flooddog/Flood-Dog-Github/Pressure Board Plate/Prerssure Mount.3mf

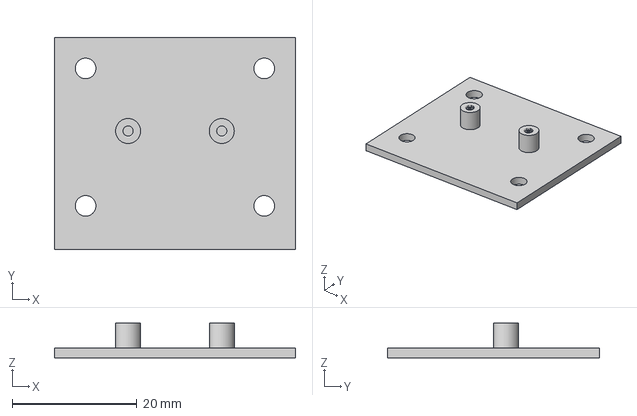
[picture p21: CAD file, 2021-11-01]
Pressure Board Plate/Prerssure Mount.3mf
38.6 x 34.0 x 5.57 mm
