flooddog/Flood-Dog-Github/Project Case_Flood Dog/Badge/Badge Template v57 v5.3mf

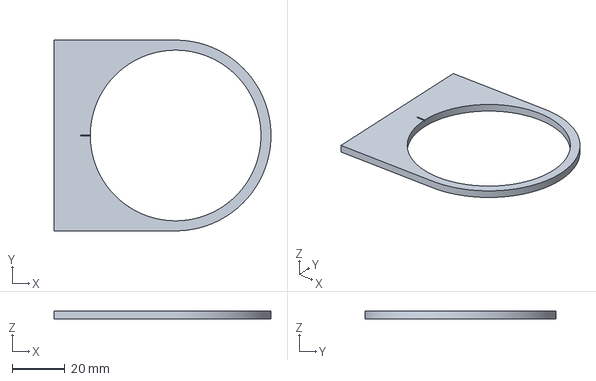
[picture p22: CAD file, 2021-12-22]
Project Case_Flood Dog/Badge/Badge Template v57 v5.3mf
81.9 x 72.0 x 3.00 mm
