flooddog/Flood-Dog-Github/Project Case_Flood Dog/Project Case_Flood Dog v53/Project Case_Flood Dog v53 v1_Left Cable Gland Cap.3mf

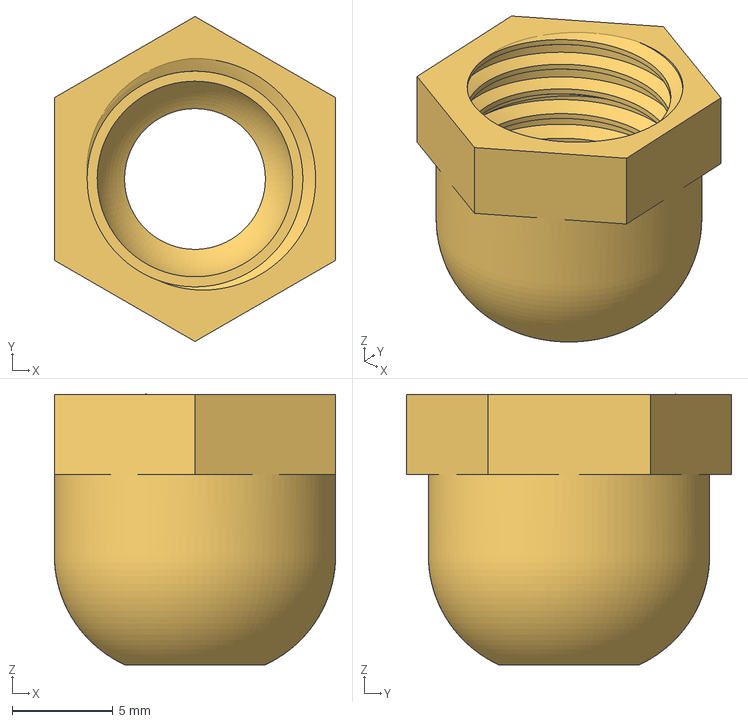
[picture p23: CAD file, 2021-11-01]
Project Case_Flood Dog/Project Case_Flood Dog v53/Project Case_Flood Dog v53 v1_Left Cable Gland Cap.3mf
14.0 x 16.2 x 13.5 mm
