flooddog/Flood-Dog-Github/Voltaics Solar Panel Frame/Voltaic Frame.3mf

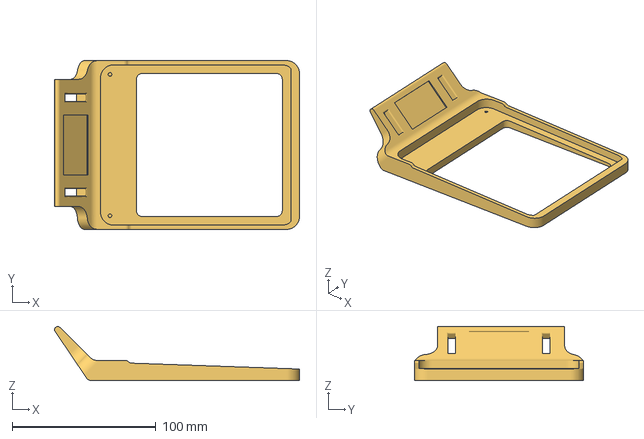
[picture p24: CAD file, 2021-11-01]
Voltaics Solar Panel Frame/Voltaic Frame.3mf
170.5 x 117.5 x 37.6 mm
