flooddog/Flood-Dog-Github/Capacitive Sensor Probe v2 v11/Component1_Cap Sensor v2 v11_Shell Top_FusionComponent.stl

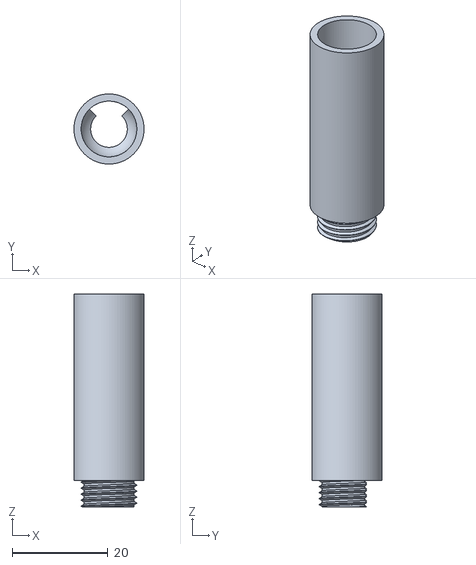
[picture p25: CAD file, 2021-06-04]
Capacitive Sensor Probe v2 v11/Component1_Cap Sensor v2 v11_Shell Top_FusionComponent.stl
14.6 x 14.6 x 44.5
