flooddog/Flood-Dog-Github/Potted Sensor/Potted Sensor v16 Stress Relief.3mf

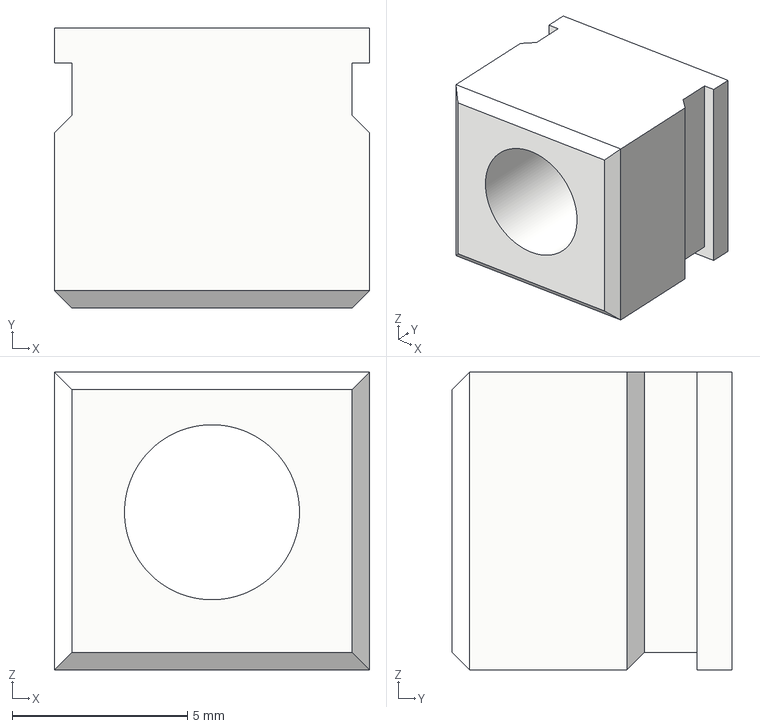
[picture p26: CAD file, 2021-12-22]
Potted Sensor/Potted Sensor v16 Stress Relief.3mf
9.00 x 8.00 x 8.50 mm
