flooddog/Flood-Dog-Github/Pressure Board Plate/Pressure Sensor Pod v4_Pressure Sensor Pod v4_Pressur Sensor Pod_1_Top_Pressur Sensor Pod.stl

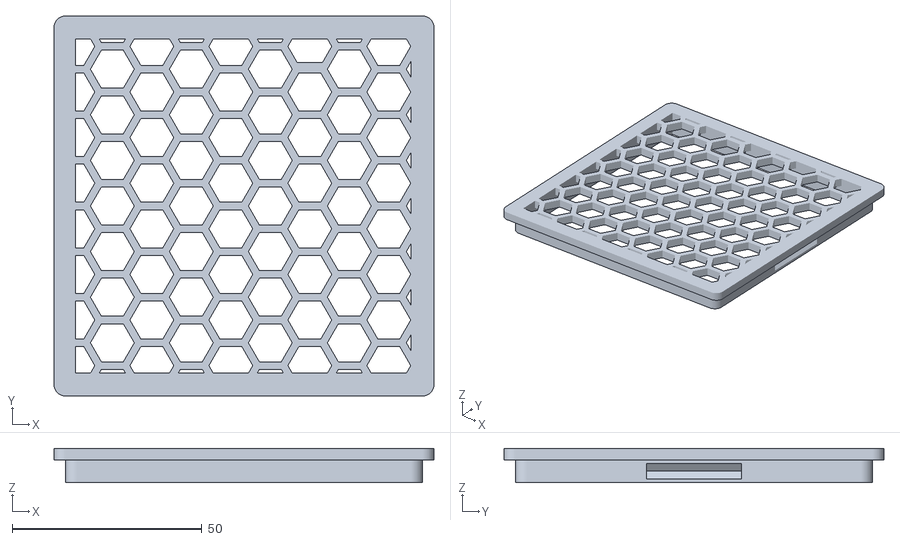
[picture p27: CAD file, 2021-11-01]
Pressure Board Plate/Pressure Sensor Pod v4_Pressure Sensor Pod v4_Pressur Sensor Pod_1_Top_Pressur Sensor Pod.stl
100.0 x 100.0 x 9.00
