flooddog/Flood-Dog-Github/Project Case_Flood Dog/Badge/Badge FD-001.3mf

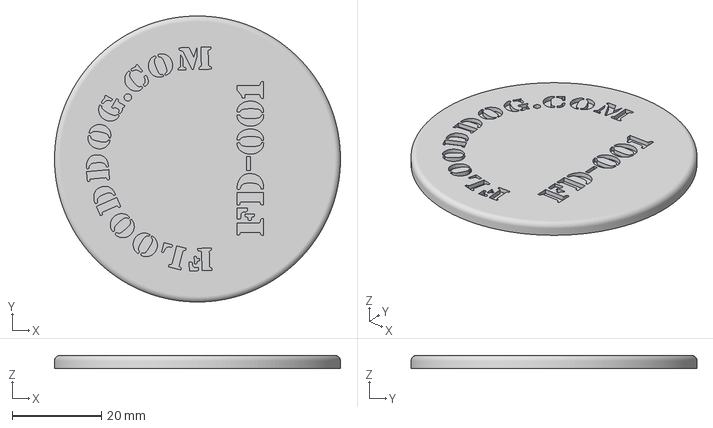
[picture p28: CAD file, 2021-12-22]
Project Case_Flood Dog/Badge/Badge FD-001.3mf
64.0 x 64.0 x 3.00 mm
