flooddog/Flood-Dog-Github/Project Case_Flood Dog/Project Case_Flood Dog v53/Project Case_Flood Dog v53 v1_Locking Cap_001.3mf

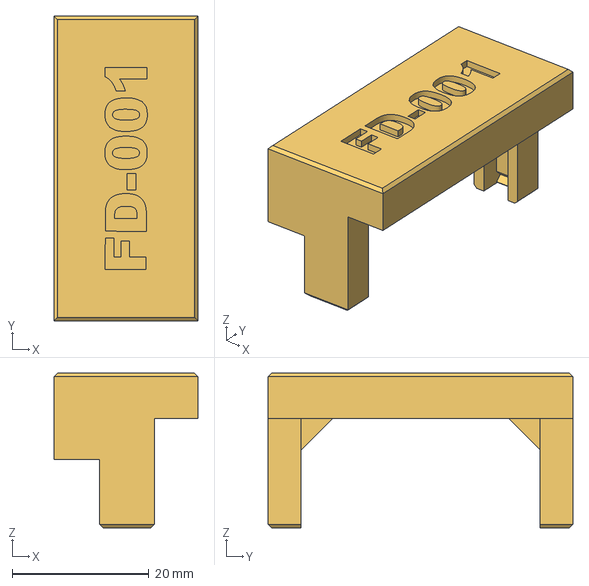
[picture p29: CAD file, 2021-11-01]
Project Case_Flood Dog/Project Case_Flood Dog v53/Project Case_Flood Dog v53 v1_Locking Cap_001.3mf
21.1 x 44.6 x 22.6 mm
