flooddog/Flood-Dog-Github/Potted Sensor/Potted Laser Sensor.3mf

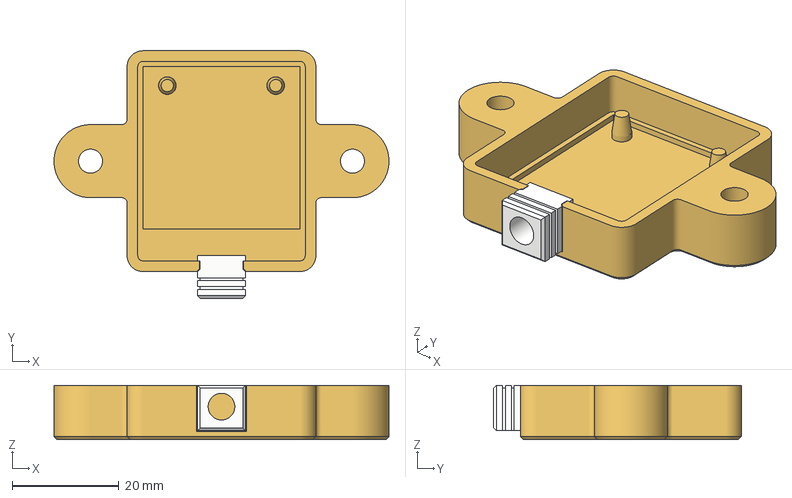
[picture p31: CAD file, 2021-12-22]
Potted Sensor/Potted Laser Sensor.3mf
62.8 x 46.4 x 10.2 mm
Case
Strain Relief
