flooddog/Flood-Dog-Github/Project Case_Flood Dog/Badge/Badge Template v58 v13.3mf

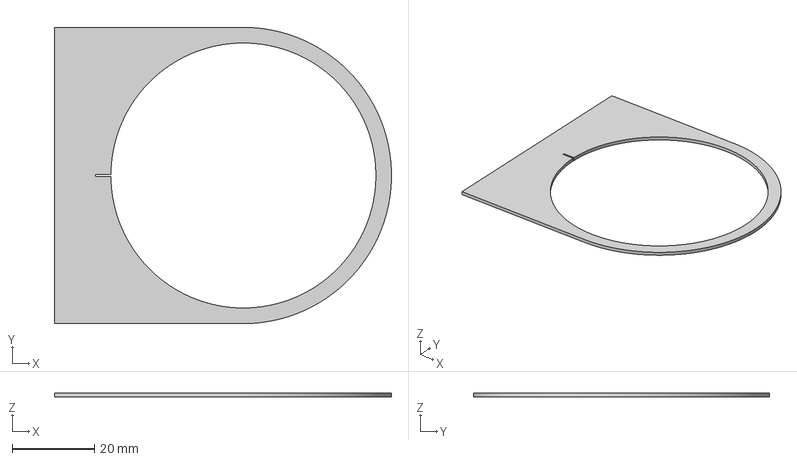
[picture p32: CAD file, 2021-12-22]
Project Case_Flood Dog/Badge/Badge Template v58 v13.3mf
81.9 x 72.0 x 1.00 mm
