flooddog/Flood-Dog-Github/Project Case_Flood Dog/Project Case_Flood Dog v53/Project Case_Flood Dog v53 v1_Mount_002.3mf

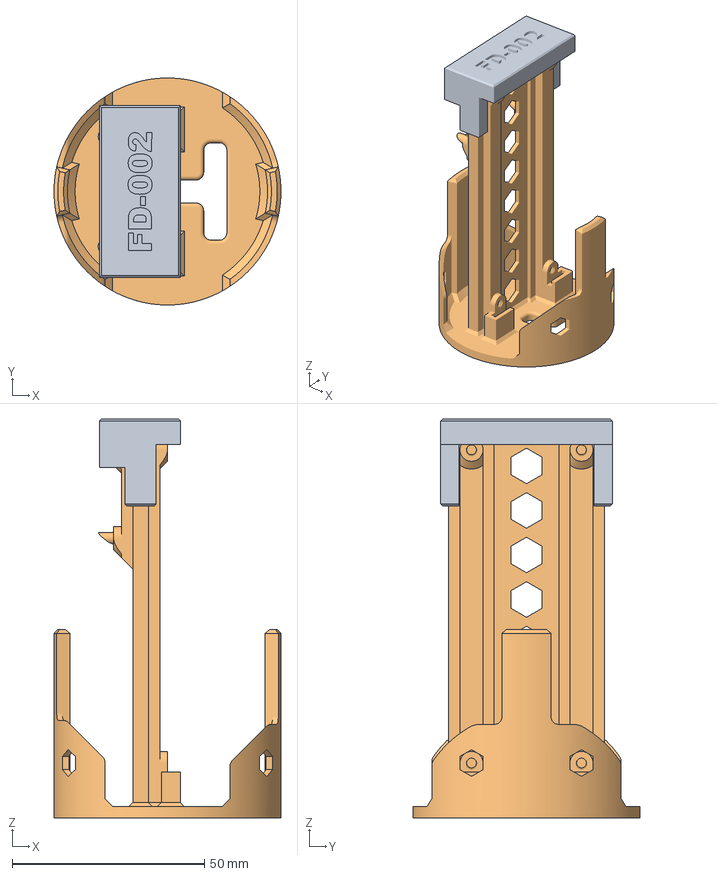
[picture p33: CAD file, 2021-11-01]
Project Case_Flood Dog/Project Case_Flood Dog v53/Project Case_Flood Dog v53 v1_Mount_002.3mf
59.0 x 59.0 x 103.7 mm
Locking Cap
Mount
