flooddog/Flood-Dog-Github/Capacitive Sensor Probe v2 v11/Component1_Cap Sensor v2 v11_Shell Bottom_FusionComponent.stl

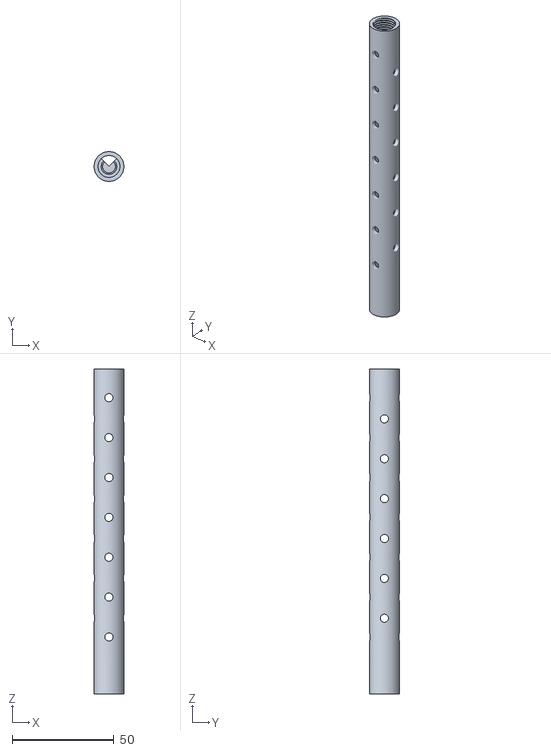
[picture p34: CAD file, 2021-06-04]
Capacitive Sensor Probe v2 v11/Component1_Cap Sensor v2 v11_Shell Bottom_FusionComponent.stl
14.6 x 14.6 x 159.5
