flooddog/Flood-Dog-Github/Potted Sensor/Project Case.3mf

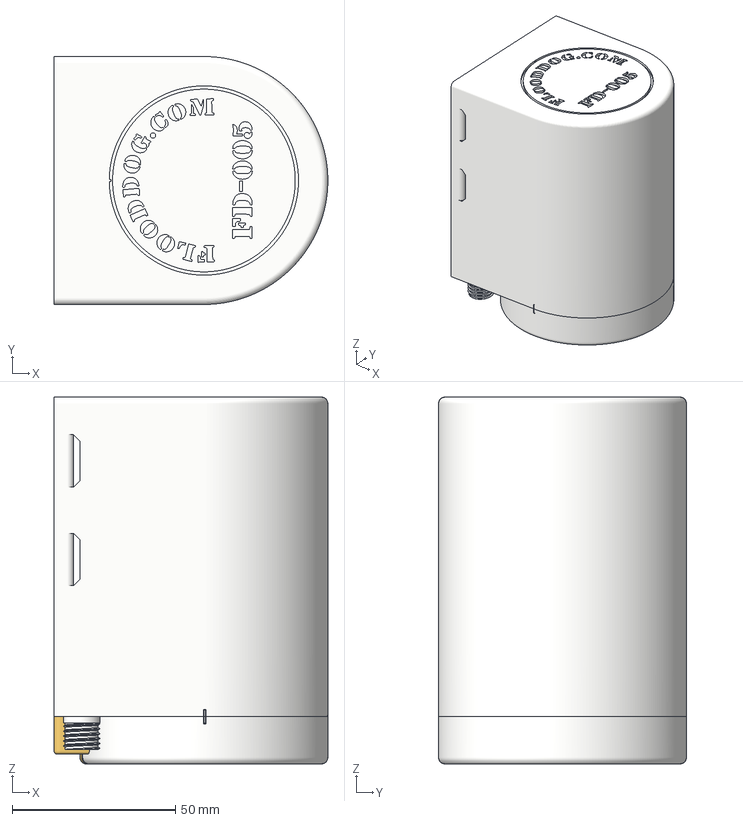
[picture p35: CAD file, 2021-12-22]
Potted Sensor/Project Case.3mf
83.9 x 76.0 x 112.5 mm
Bottom
Locking Pin
Top
