flooddog/Flood-Dog-Github/Project Case_Flood Dog/Project Case_Flood Dog v53/Project Case_Flood Dog v53 v1_Right Wire Wrap.3mf

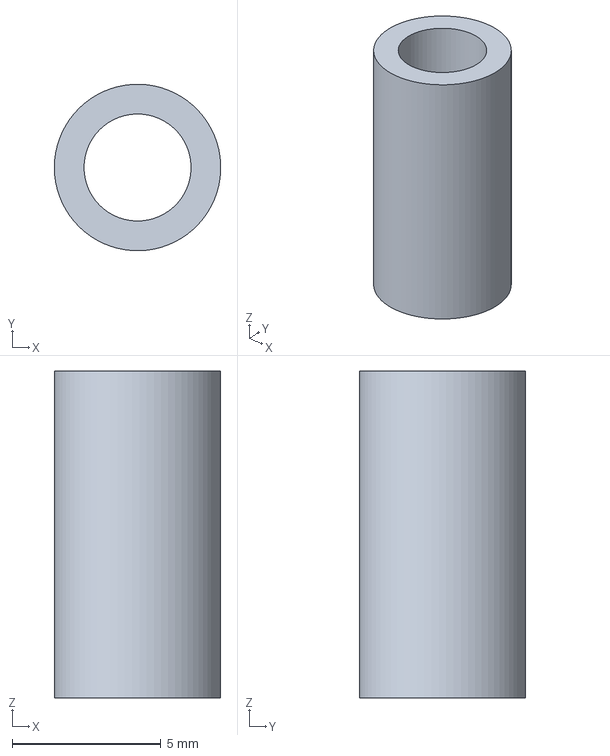
[picture p36: CAD file, 2021-11-01]
Project Case_Flood Dog/Project Case_Flood Dog v53/Project Case_Flood Dog v53 v1_Right Wire Wrap.3mf
5.60 x 5.60 x 11.0 mm
