flooddog/Flood-Dog-Github/Capacitive Sensor Probe v2 v11/Component1_Cap Sensor v2 v11_Sensor_FusionComponent.stl

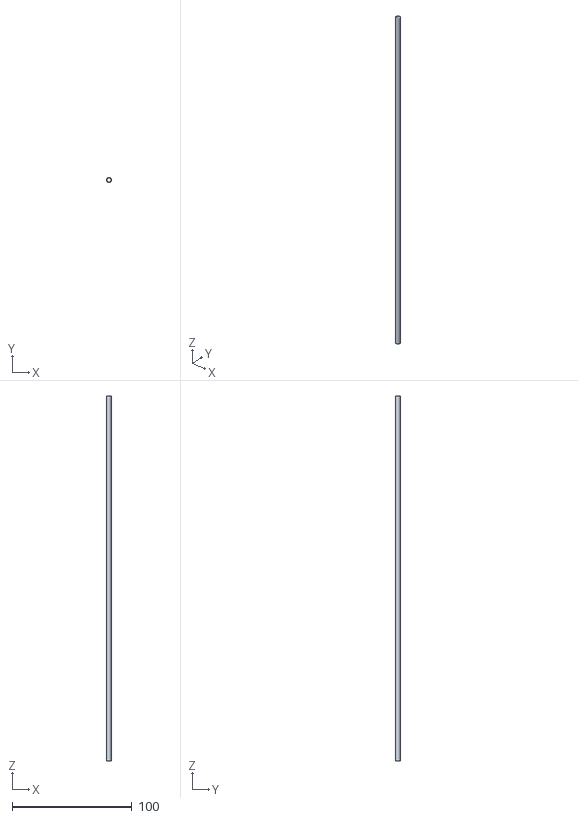
[picture p37: CAD file, 2021-06-04]
Capacitive Sensor Probe v2 v11/Component1_Cap Sensor v2 v11_Sensor_FusionComponent.stl
3.97 x 3.96 x 304.8
