flooddog/Flood-Dog-Github/Project Case_Flood Dog/Project Case_Flood Dog v53/Project Case_Flood Dog v53 v1_Bottom.3mf

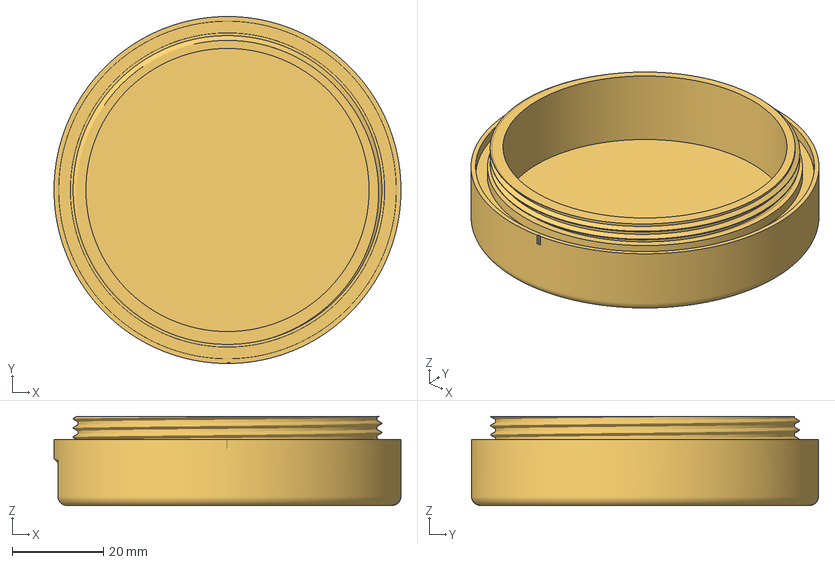
[picture p38: CAD file, 2021-11-01]
Project Case_Flood Dog/Project Case_Flood Dog v53/Project Case_Flood Dog v53 v1_Bottom.3mf
76.0 x 76.0 x 19.5 mm
