flooddog/Flood-Dog-Github/Capacitive Sensor Probe v2 v11/Component1_Cap Sensor v2 v11_Segment_FusionComponent.stl

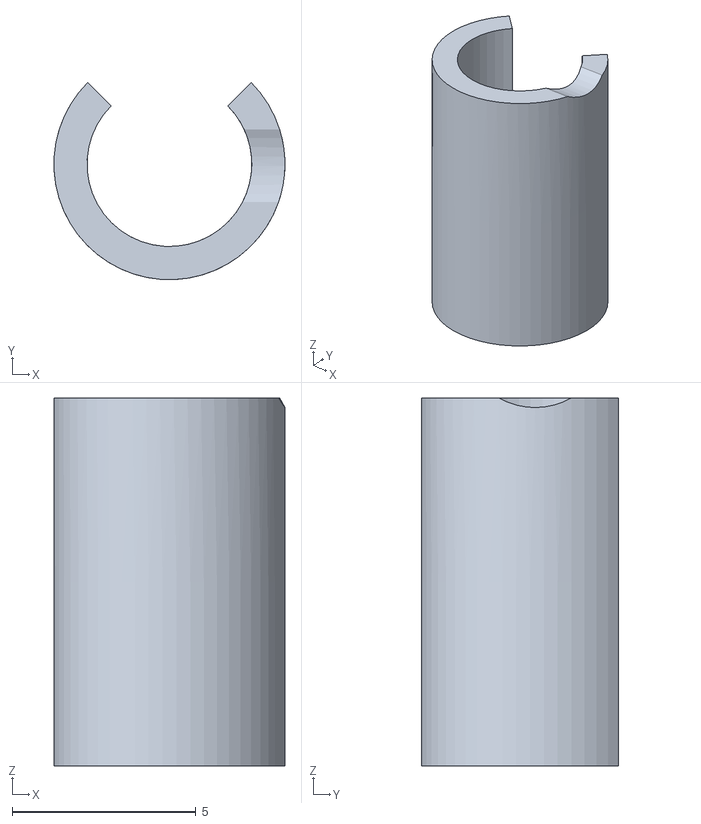
[picture p39: CAD file, 2021-06-04]
Capacitive Sensor Probe v2 v11/Component1_Cap Sensor v2 v11_Segment_FusionComponent.stl
6.28 x 5.36 x 10.0
