flooddog/Flood-Dog-Github/Project Case_Flood Dog/Project Case_Flood Dog v53/Project Case_Flood Dog v53 v1_Right Cable Gland Inner Seal.3mf

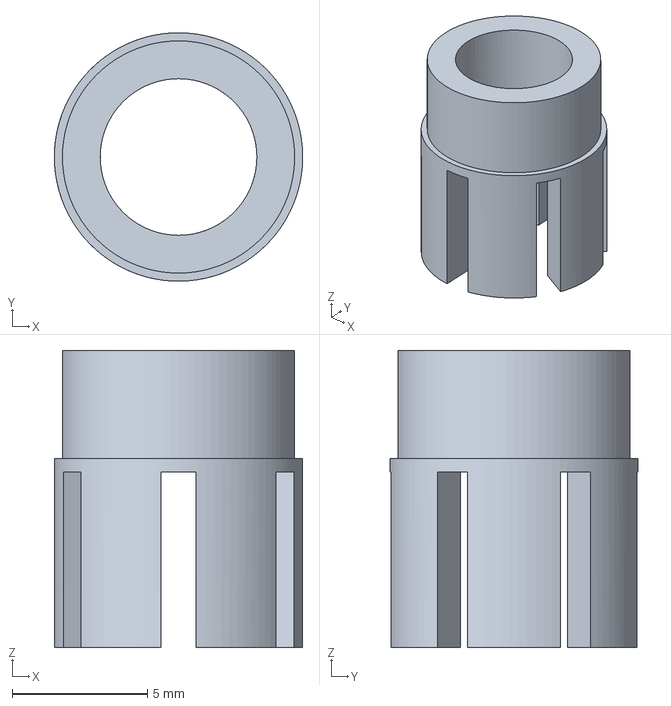
[picture p43: CAD file, 2021-11-01]
Project Case_Flood Dog/Project Case_Flood Dog v53/Project Case_Flood Dog v53 v1_Right Cable Gland Inner Seal.3mf
9.20 x 9.20 x 11.0 mm
