flooddog/Flood-Dog-Github/Project Case_Flood Dog/Project Case_Flood Dog v53/Project Case_Flood Dog v53 v1_Locking Pin_Dog Dev.3mf

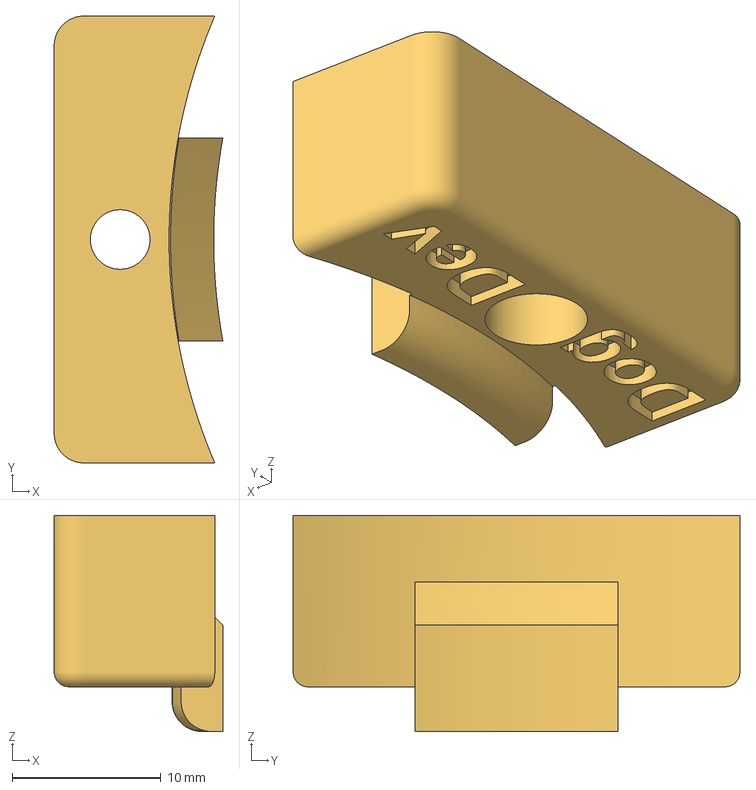
[picture p44: CAD file, 2021-11-01]
Project Case_Flood Dog/Project Case_Flood Dog v53/Project Case_Flood Dog v53 v1_Locking Pin_Dog Dev.3mf
11.3 x 30.0 x 14.5 mm
