flooddog/Flood-Dog-Github/Cap_Water_Sensor_Eagle/GWLSensorv3.brd

## EAGLE design Capacitive_Water_Sensor_Eagle/_archive/GWLSensorv3.brd (2021-06-30, an earlier design)

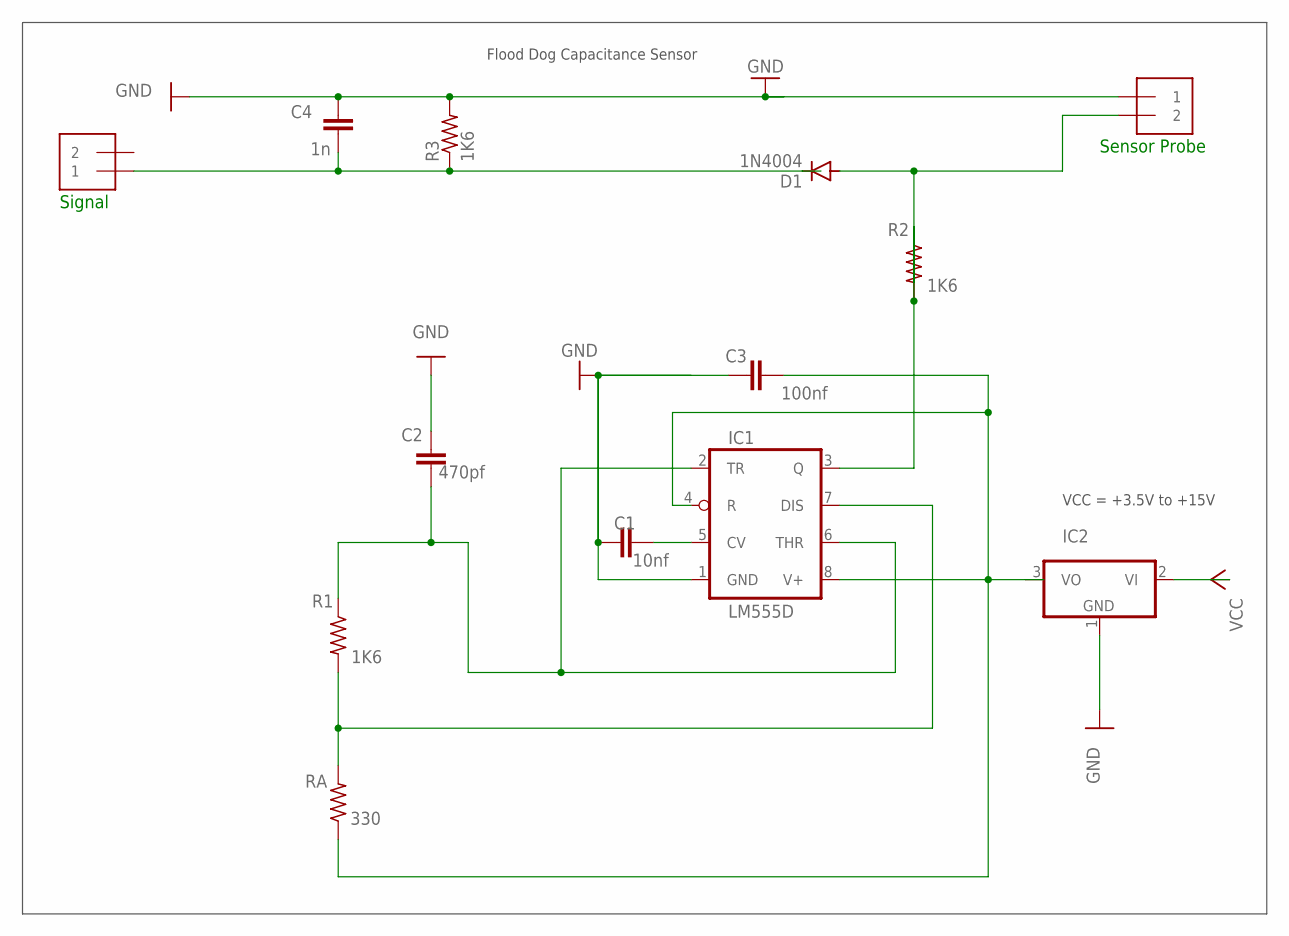
[picture p55: schematic GWLSensorv3.sch]

Parts:
C1: 10nf; C0805
C2: 470pf; C0805
C3: 100nf; C0805
C4: 1n; C0805
D1: 1N4004; DO41-10
IC1: LM555D; SO08
IC2: 79L15Z; TO92
PROBE: 1X2-3.5MM
R1, R2, R3: 1K6; R0805
RA: 330; R0805
SIGNAL: 1X2-3.5MM

Connections:
GND: C1.1, C2.1, C3.1, C4.2, IC1.1 (GND), IC2.1 (GND), PROBE.1, R3.2
unnamed: C4.1, D1.C, R3.1, SIGNAL.1
unnamed: C2.2, IC1.2 (TR), IC1.6 (THR), R1.1
unnamed: IC1.7 (DIS), R1.2, RA.2
unnamed: C1.2, IC1.5 (CV)
unnamed: D1.A, IC1.3 (Q), PROBE.2, R2.1, R2.2
unnamed: C3.2, IC1.4 (R), IC1.8 (V+), IC2.3 (VO), RA.1
VCC: IC2.2 (VI)

Notes on the sheet:
Flood Dog Capacitance Sensor
VCC = +3.5V to +15V
Signal
Sensor Probe

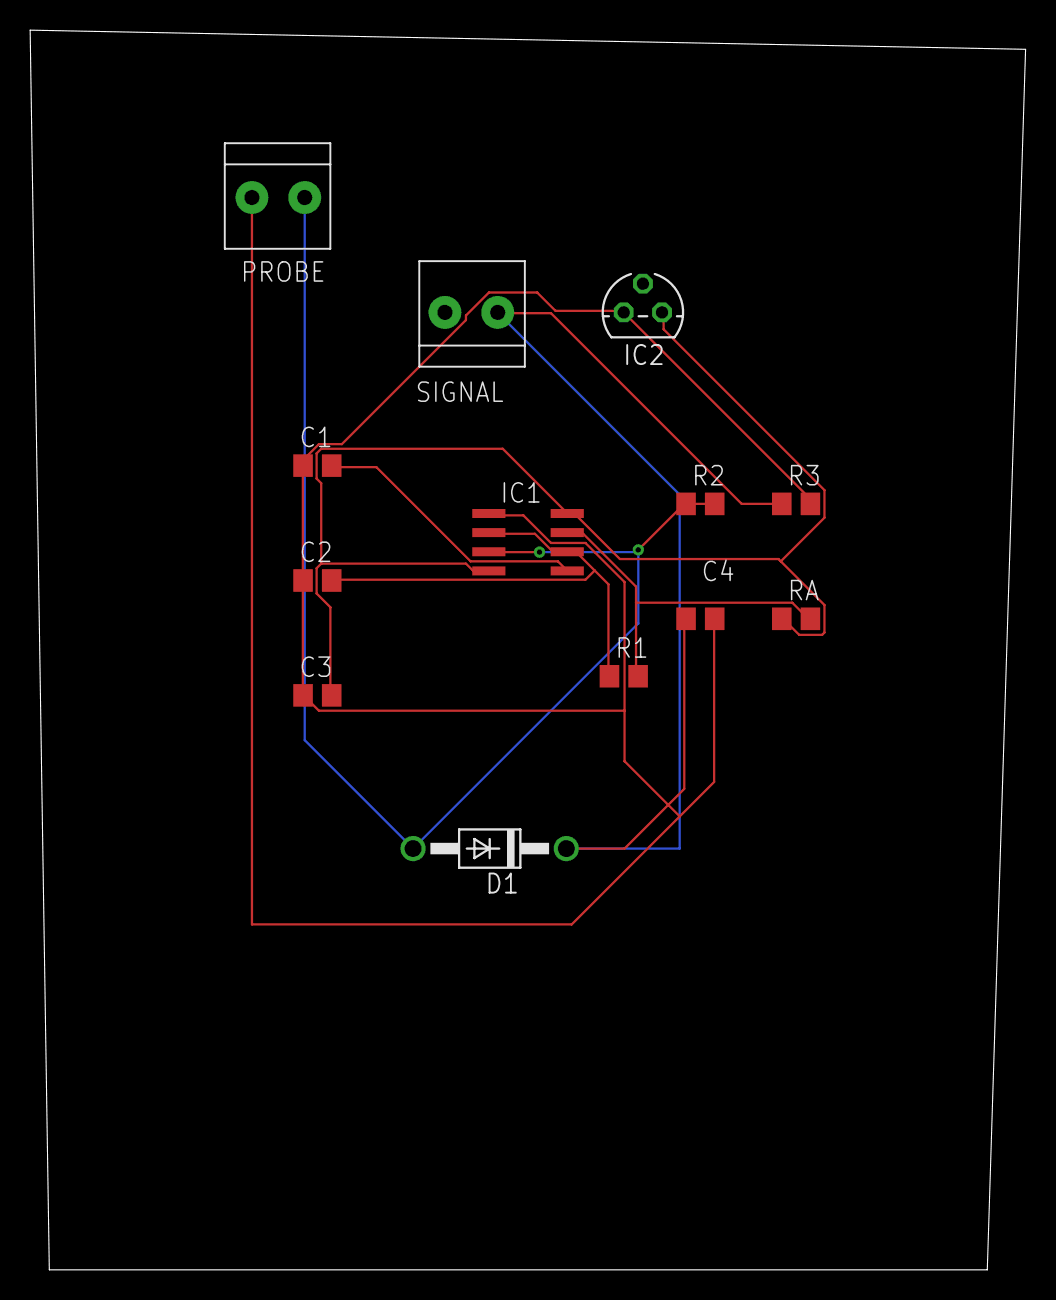
[picture p56: board GWLSensorv3.brd from above]

Board: 2 copper layers, 66.0 x 82.2 mm, 13 parts (0 on the bottom side), 7 nets.
