flooddog/Flood-Dog-Github/Flood_Dog Firmware/Flood_Dog_v07/src/sys_status.h

#ifndef SYS_STATUS_H
#define SYS_STATUS_H

#include "Particle.h"

struct systemStatus_structure {  
  uint8_t structuresVersion;                        // Version of the data structures (system and data)
  uint8_t placeholdervalue;                         // For future use
  bool verboseCounts;                               // Tells us if we are sending verbose count webhooks
  bool connectedStatus;                             // Are we connected?
  bool verboseMode;                                 // Turns on extra messaging
  bool solarPowerMode;                              // Powered by a solar panel or utility power
  bool lowPowerMode;                                // Does the device need to run disconnected to save battery
  uint8_t lowBatteryMode;                           // Is the battery level so low that we can no longer connect
  int stateOfCharge;                                // Battery charge level
  uint8_t batteryState;                             // Stores the current battery state
  int resetCount;                                   // reset count of device (0-256)
  float timezone;                                   // Time zone value -12 to +12
  float dstOffset;                                  // How much does the DST value change?
  uint8_t openTime;                                 // Hour the park opens (0-23)
  uint8_t closeTime;                                // Hour the park closes (0-23)
  unsigned long lastHookResponse;                   // Last time we got a valid Webhook response
  unsigned long lastConnection;                     // Last time we successfully connected to Particle
  uint16_t lastConnectionDuration;                  // How long - in seconds - did it take to last connect to the Particle cloud
uint8_t sensorType;                               // What is the sensor type - 0-Pressure Sensor, 1-PIR Sensor
};

extern struct systemStatus_structure sysStatus;

extern bool systemStatusWriteNeeded;               // Keep track of when we need to write

#endif
