flooddog/Flood-Dog-Github/Flood_Dog Firmware/Flood_Dog_v07/src/3rdGenDevicePinoutdoc.h

/**********************************************************************************************************************
 *
 * Left Side (16 pins)
 * !RESET -
 * 3.3V -
 * !MODE -
 * GND -
 * A0 -
 * A1 -
 * A2 -
 * A3 -
 * A4 -
 * A5 / SPI SS -
 * SCK - SPI Clock
 * MO - SPI MOSI
 * MI - SPI MISO
 * UART RX -
 * UART TX -

 Right Size (12 pins)
 * Li+
 * ENABLE
 * VUSB -
 * D8 - Wake Connected to Watchdog Timer
 * D7 - Blue Led
 * D6 - DEEP-SLEEP Enable Pin - Brings Enable Pin low - Only RTC Alarm interrupt will wake
 * D5 - NC
 * D4 - User Switch
 * D3 - NC
 * D2 - NC
 * SCL - I2C Clock - FRAM
 * SDA - I2C Data - FRAM
 *
 *
***********************************************************************************************************************/


/**
 * @file   3rdGenDevicePinoutdoc.h
 * @author Chip McClelland
 * @date   1-24-2020
 * @brief  File containing the pinout documentation for 3rd Generation Particle Devices.
 * */
